ElKinoflop/Blatherskite/case files/Blatherskite 7 - Mid Lower PR.dxf

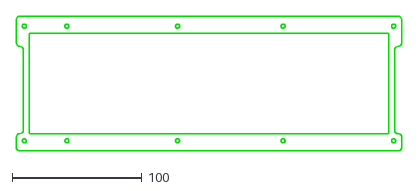
[picture p26: CAD file, 2025-02-03, an earlier design]
case files/Blatherskite 7 - Mid Lower PR.dxf
296.9 x 103.7
