ElKinoflop/Blatherskite/case files/Blatherskite 8 - Bottom PR.dxf

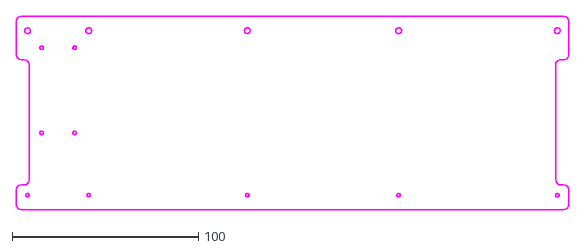
[picture p27: CAD file, 2025-02-03, an earlier design]
case files/Blatherskite 8 - Bottom PR.dxf
296.9 x 103.7
