ElKinoflop/Blatherskite/case files/Blatherskite 4 - Plate Layer.dxf

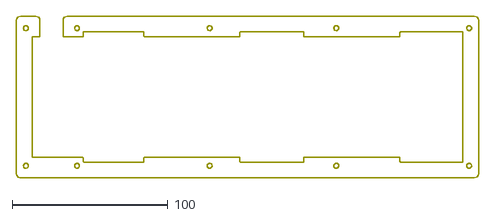
[picture p28: CAD file, 2025-01-30, an earlier design]
case files/Blatherskite 4 - Plate Layer.dxf
296.9 x 103.7
