ElKinoflop/Blatherskite/case files/Blatherskite 1 - Top.dxf

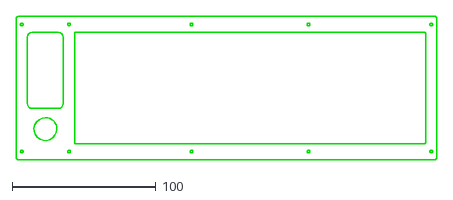
[picture p29: CAD file, 2025-01-30, an earlier design]
case files/Blatherskite 1 - Top.dxf
292.6 x 99.5
